efyang/dovetail-kb/outlines/reset_nub_stage1.dxf

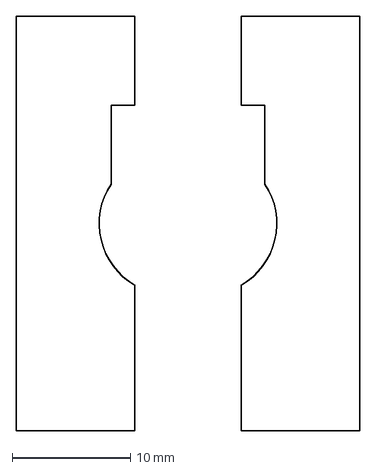
[picture p23: CAD file, 2022-07-27]
outlines/reset_nub_stage1.dxf
29.0 x 35.0 mm
